Frederic98/LMI-Restore/LMI_GUI/Images/nut.jpg

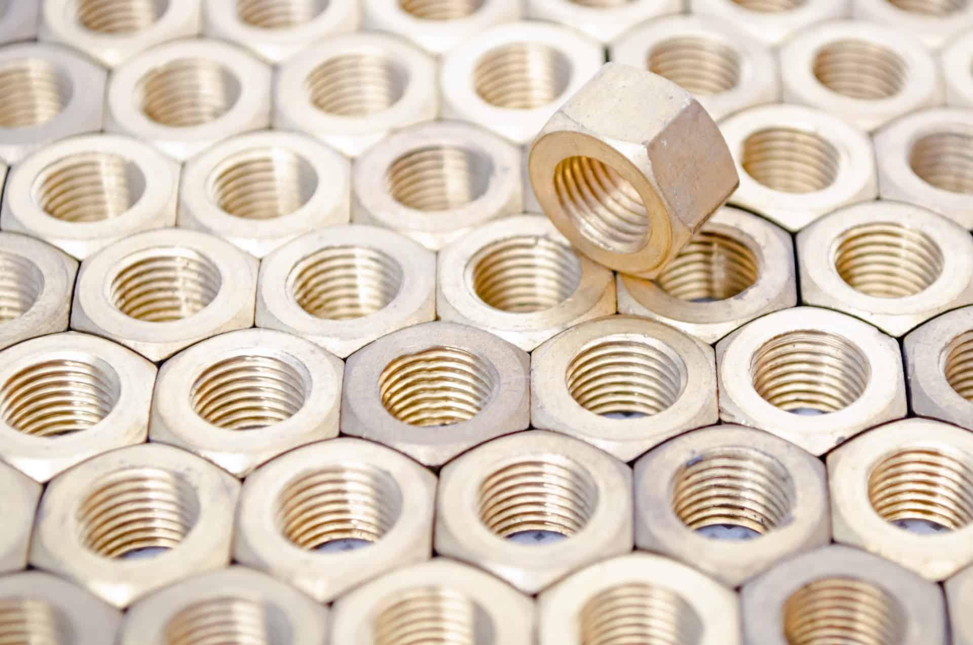
LMI_GUI/Images/nut.jpg
