Frederic98/LMI-Restore/LMI_GUI/Images/busy_1.PNG

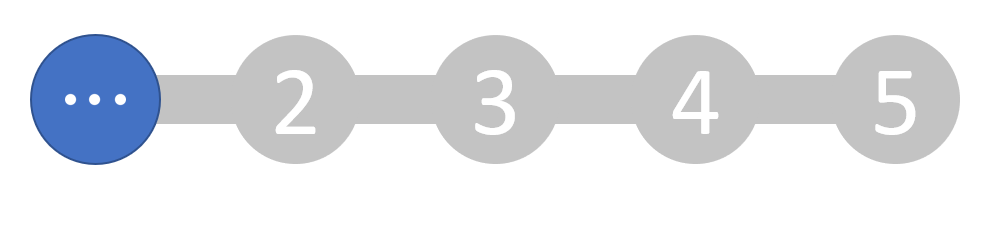
LMI_GUI/Images/busy_1.PNG
