Frederic98/LMI-Restore/LMI_GUI/Images/busy_3.PNG

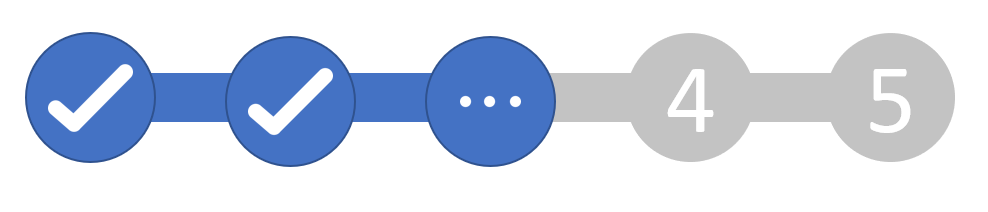
LMI_GUI/Images/busy_3.PNG
