Frederic98/LMI-Restore/LMI_GUI/Images/Storage unit empty robot side.png

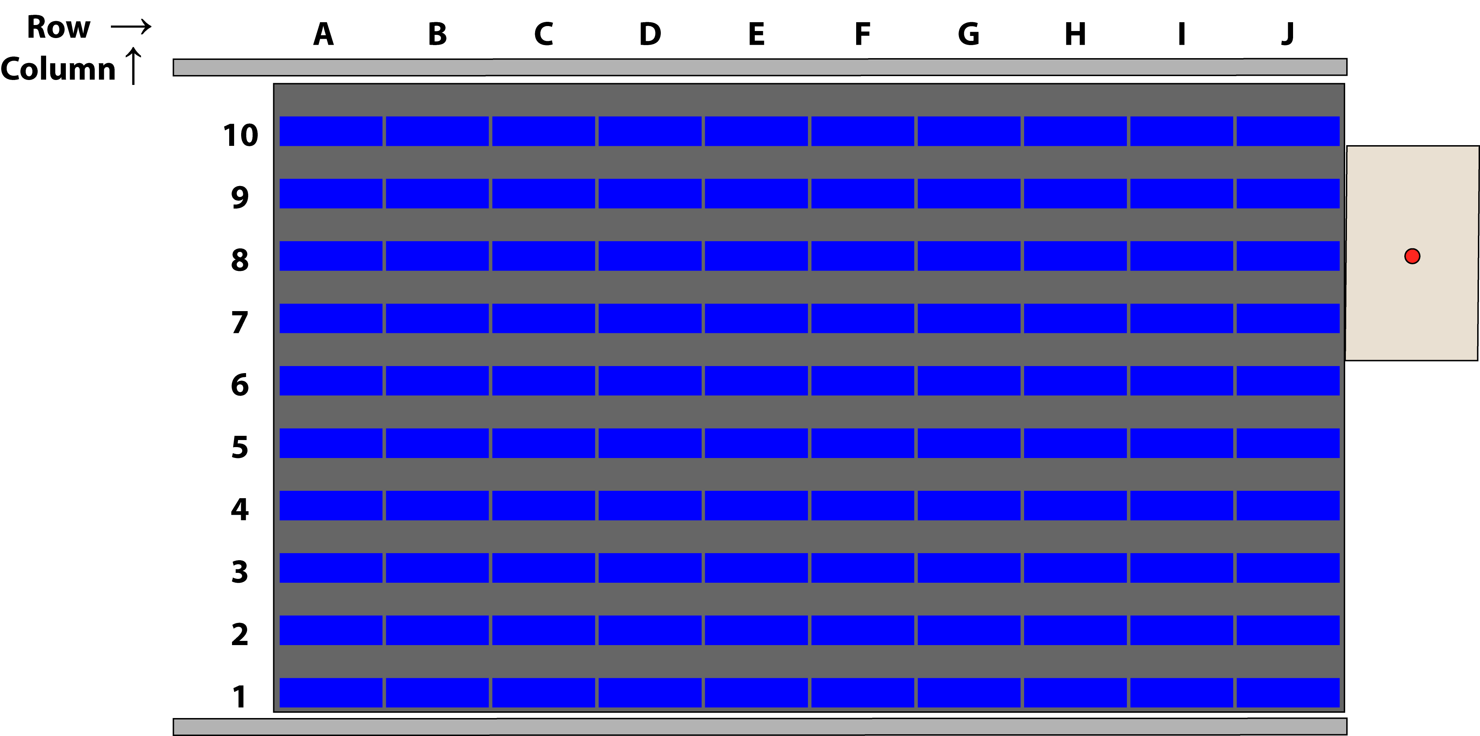
LMI_GUI/Images/Storage unit empty robot side.png
