Frederic98/LMI-Restore/LMI_GUI/Images/Triple-dot.png

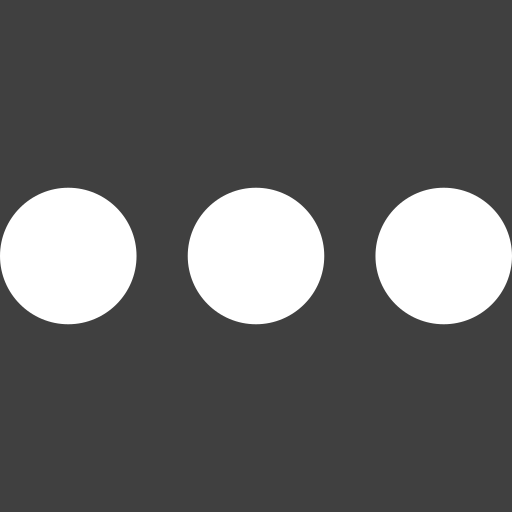
LMI_GUI/Images/Triple-dot.png
