Frederic98/LMI-Restore/CAD Files/CAD LMI/3D machining files/T00151-03D-R01.STL

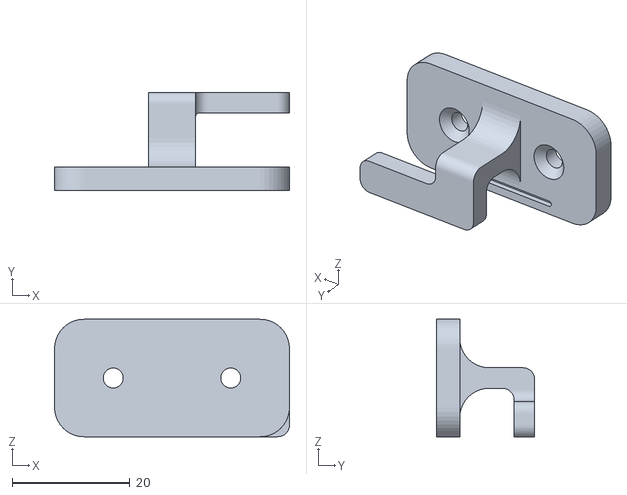
[picture p48: CAD file, 2019-02-02]
CAD Files/CAD LMI/3D machining files/T00151-03D-R01.STL
40.0 x 16.8 x 20.0
