Frederic98/LMI-Restore/CAD Files/CAD LMI/DXF/T00140-0A4-R00-1v1.DXF

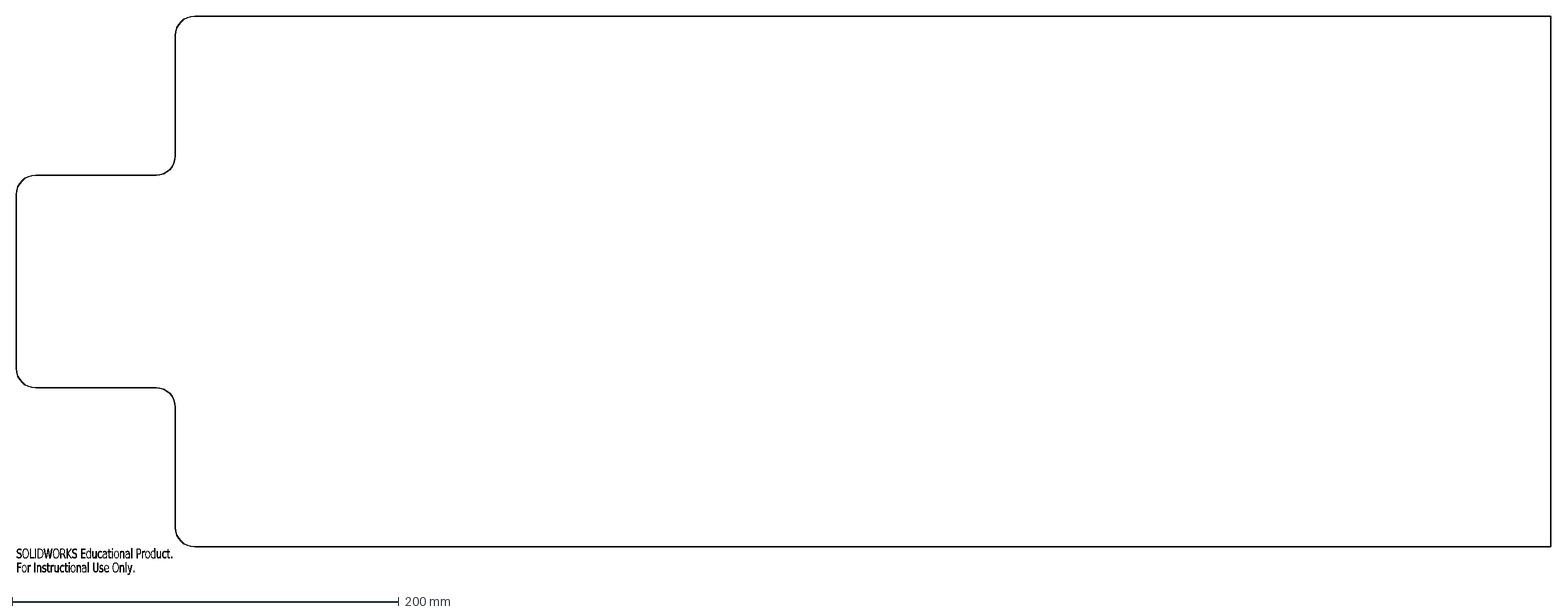
[picture p49: CAD file, 2019-02-02]
CAD Files/CAD LMI/DXF/T00140-0A4-R00-1v1.DXF
SOLIDWORKS Educational Product.
For Instructional Use Only.
