Frederic98/LMI-Restore/LMI_GUI/Images/verify-sign.png

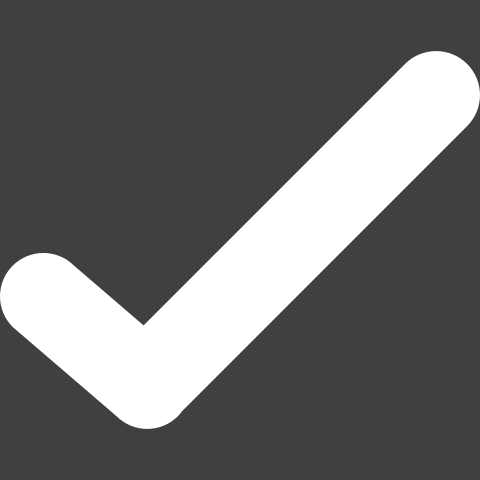
LMI_GUI/Images/verify-sign.png
