Frederic98/LMI-Restore/LMI_GUI/Images/verify-sign_green.png

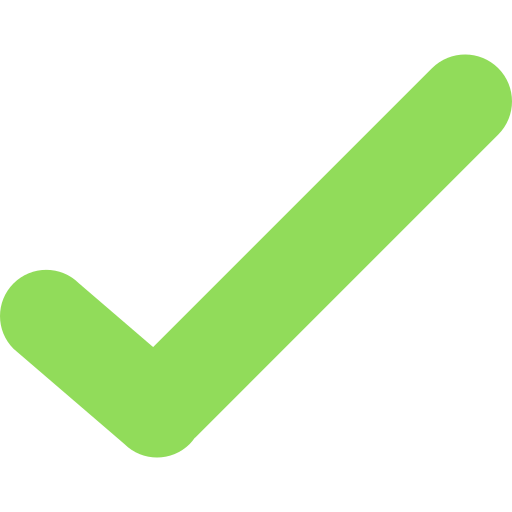
LMI_GUI/Images/verify-sign_green.png
