Frederic98/LMI-Restore/CAD Files/CAD LMI/Drawings/T00155-0A3-R00.pdf

37,50 | 15

200

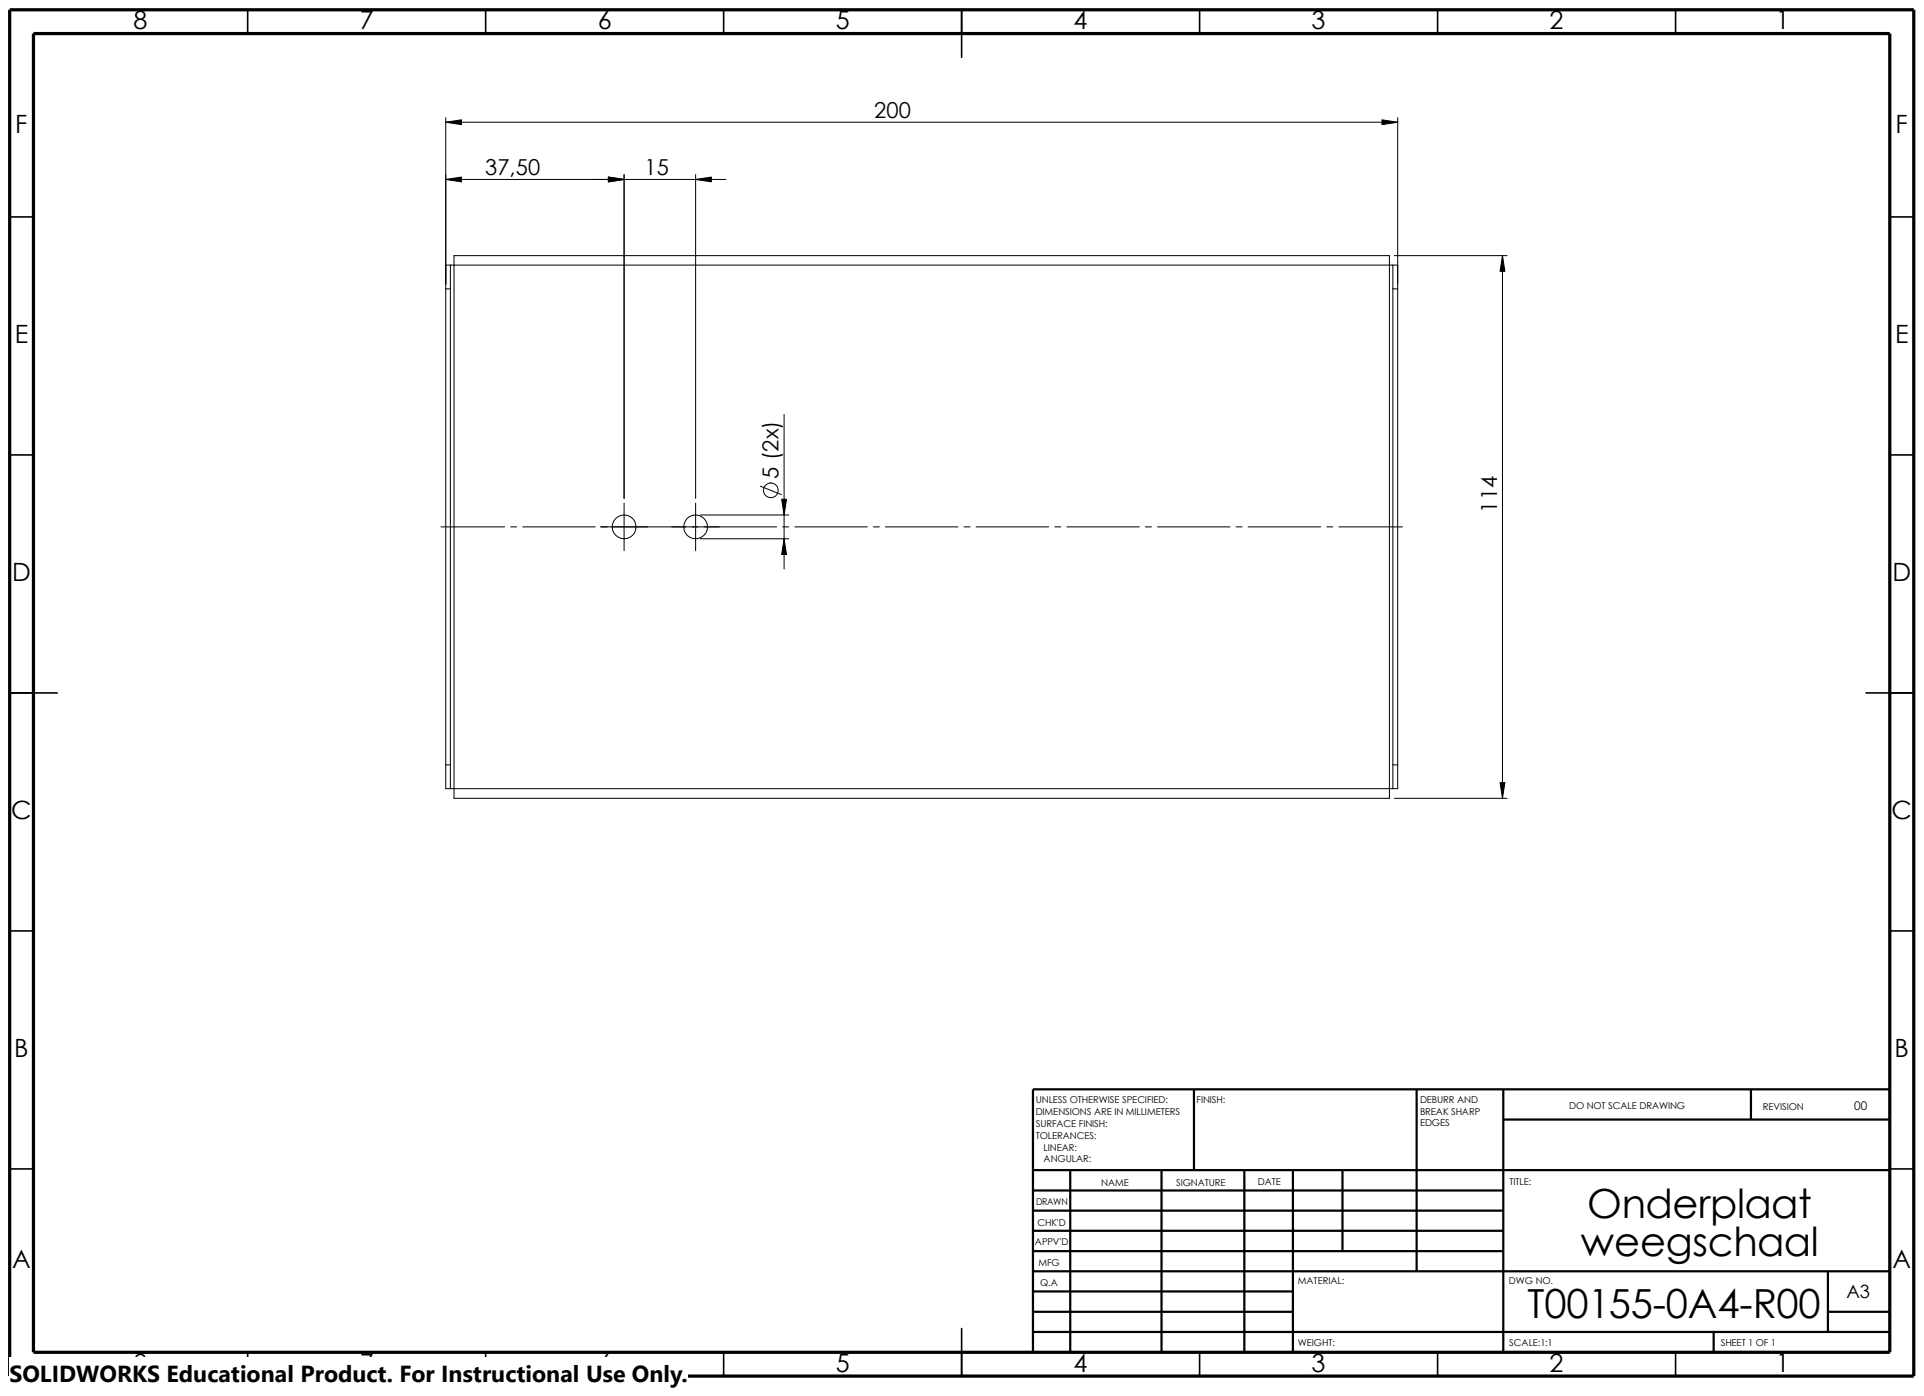
[picture p75: page 1]
SCALE:1:1; SHEET 1 OF 1; WEIGHT:; BREAK SHARP; weegschaal A; REVISION; FINISH:; EDGES; DEBURR AND

UNLESS OTHERWISE SPECIFIED:
DIMENSIONS ARE IN MILLIMETERS
SURFACE FINISH:
TOLERANCES:
LINEAR:
ANGULAR:

DO NOT SCALE DRAWING

NAME | SIGNATURE | DATE | | | | TITLE: Onderplaat

DRAWN

CHK'D

APPV'D

MFG

Q.A | | | | MATERIAL: | DWG NO. T00155-0A4-R00 | A3

SOLIDWORKS Educational Product. For Instructional Use Only.
