Frederic98/LMI-Restore/CAD Files/CAD LMI/Drawings/T00161-0A4-R00.pdf

3
2

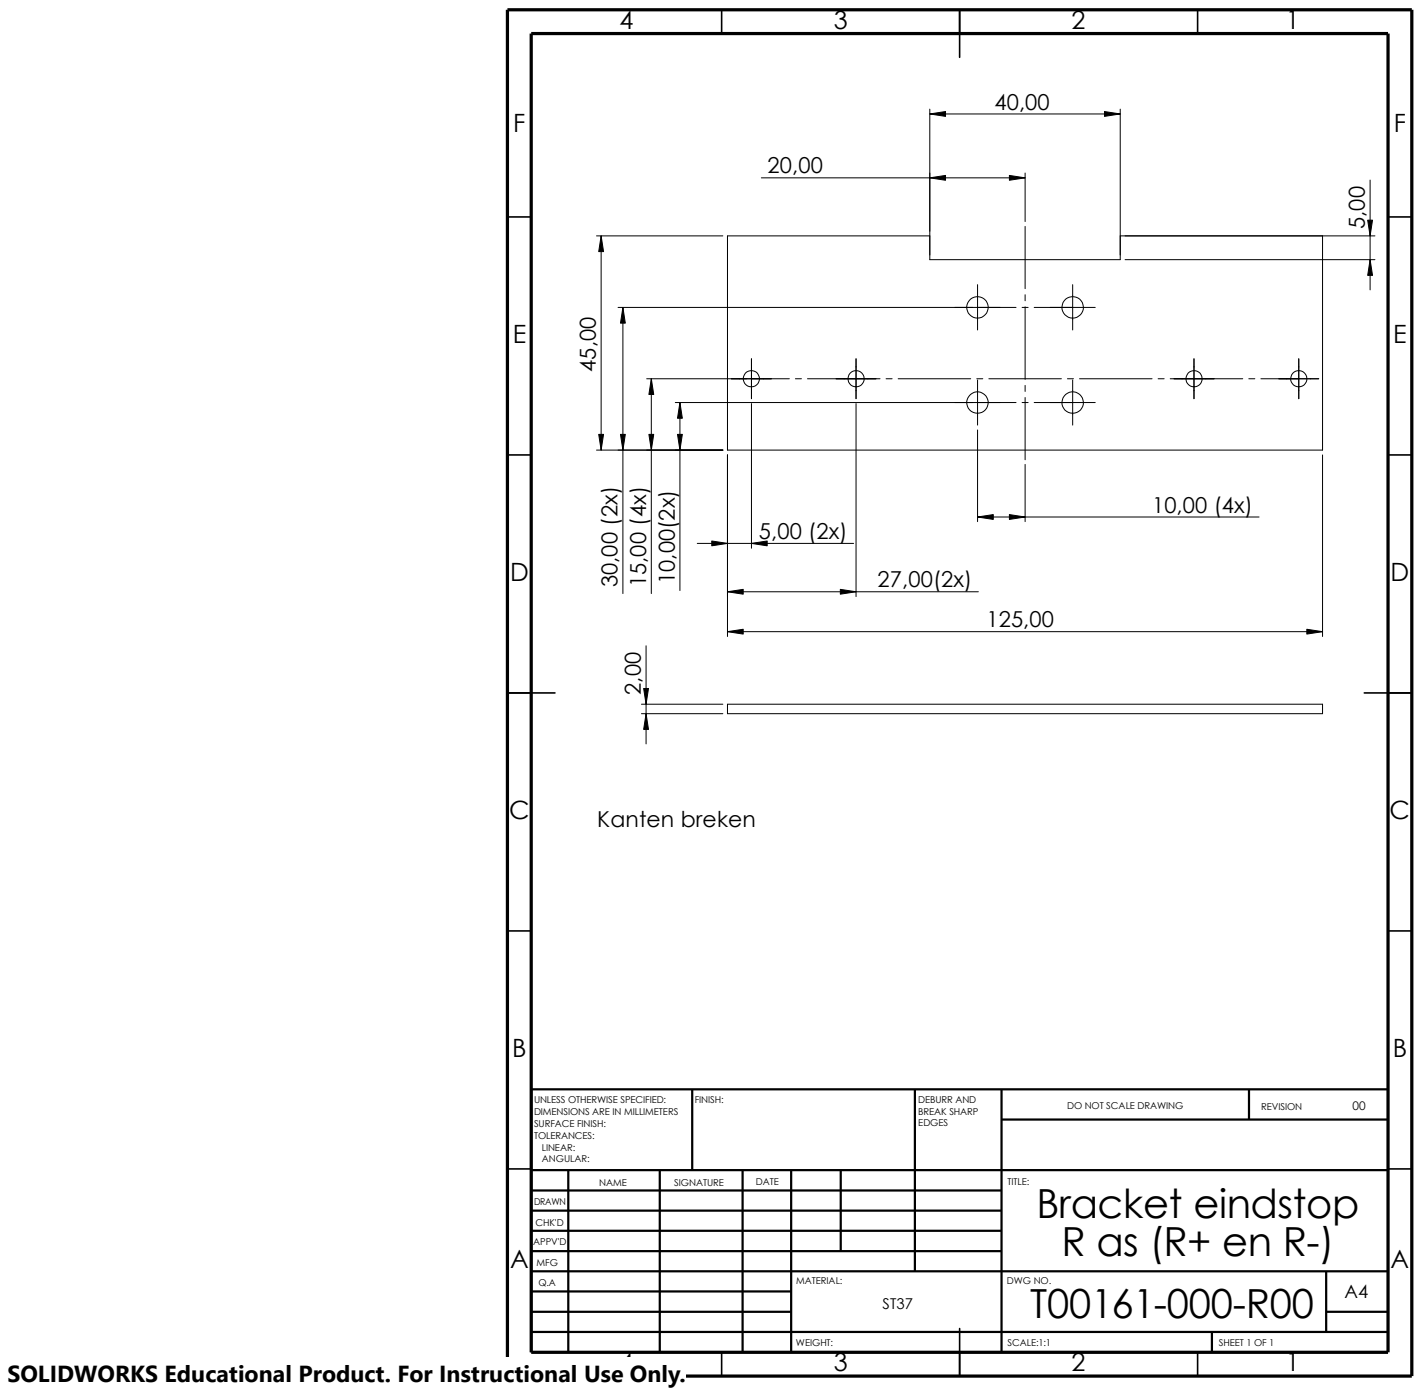
[picture p76: page 1]
Kanten breken; REVISION; DWG NO.; MFG; FINISH:; EDGES; MATERIAL:; SHEET 1 OF 1; SCALE:1:1; WEIGHT:; BREAK SHARP; DEBURR AND

UNLESS OTHERWISE SPECIFIED:
DIMENSIONS ARE IN MILLIMETERS
SURFACE FINISH:
TOLERANCES:
LINEAR:
ANGULAR:

DO NOT SCALE DRAWING

NAME | SIGNATURE | DATE | TITLE: Bracket eindstop R as (R+ en R-)

DRAWN

CHK'D

APPV'D

SOLIDWORKS Educational Product. For Instructional Use Only.
