Frederic98/LMI-Restore/CAD Files/CAD LMI/Drawings/T00167-0A4-R00.pdf

E E

F F

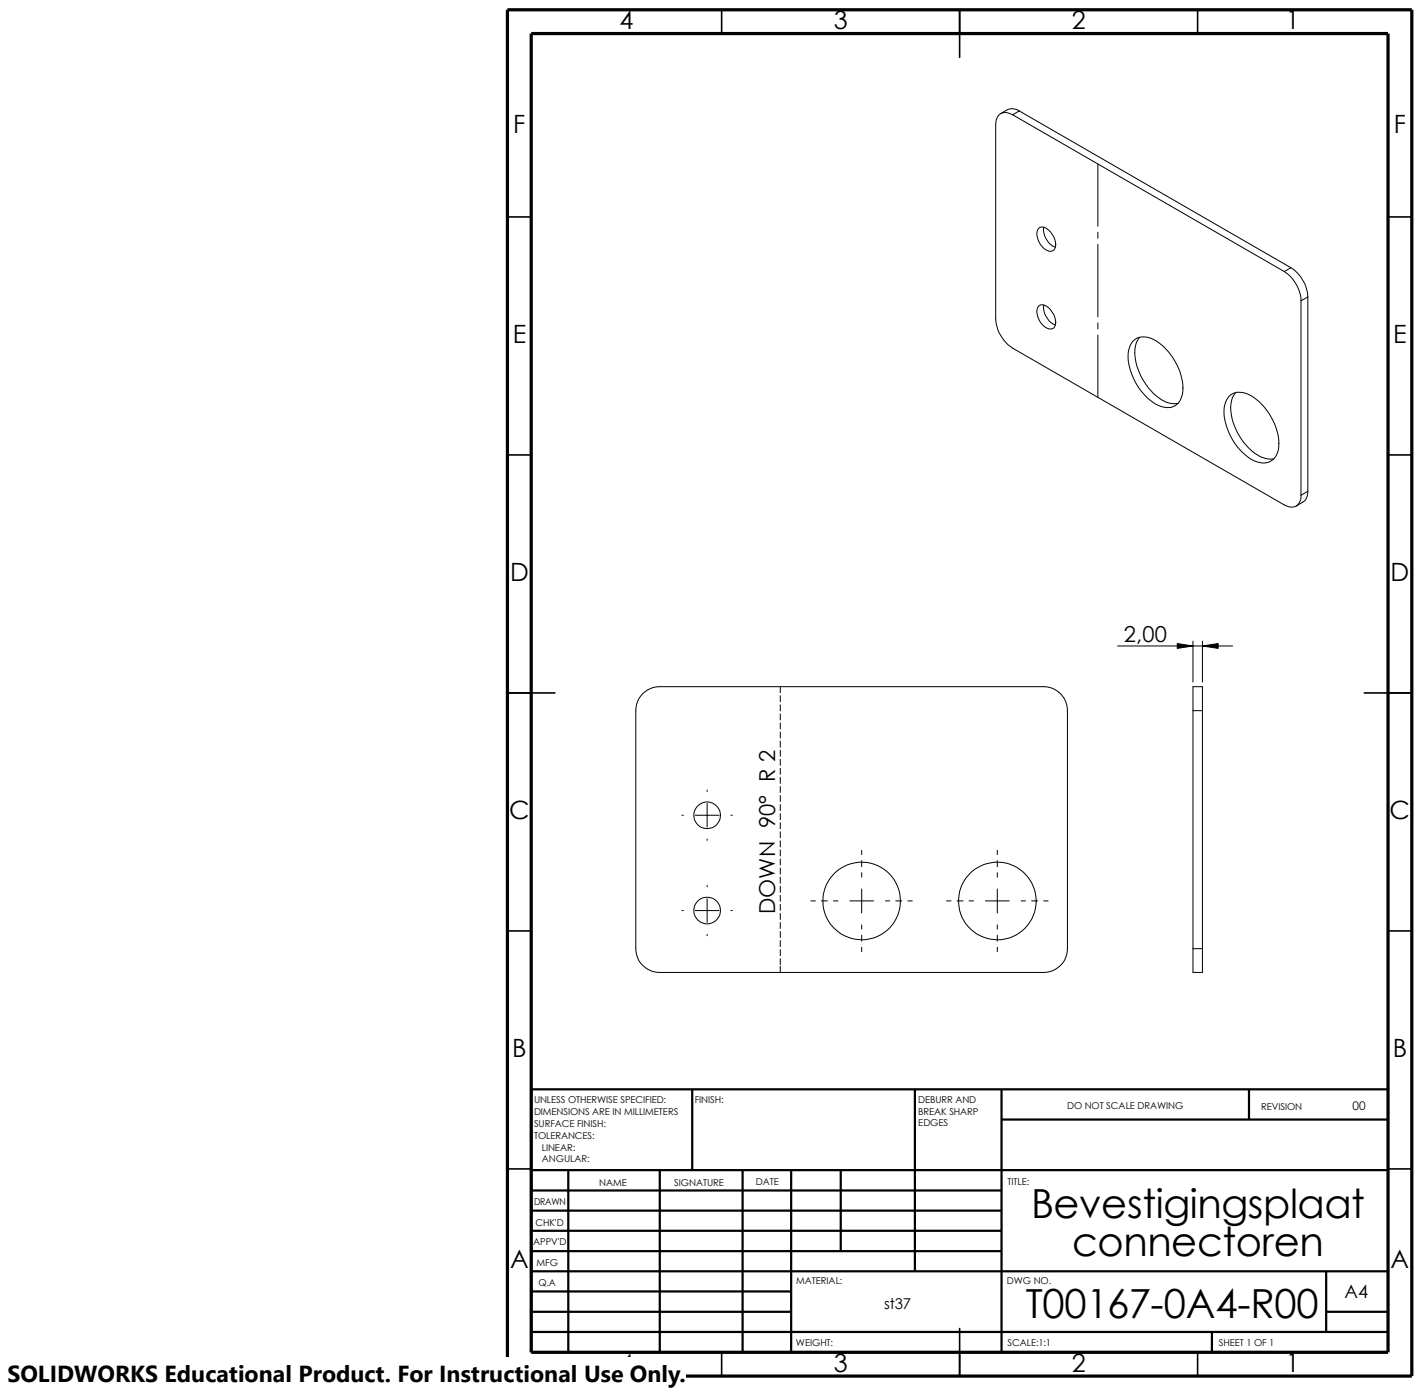
[picture p77: page 1]
BREAK SHARP; connectoren; SCALE:1:1; WEIGHT:; FINISH:; EDGES; SHEET 1 OF 1; REVISION; DEBURR AND; DOWN 90° R 2

UNLESS OTHERWISE SPECIFIED:
DIMENSIONS ARE IN MILLIMETERS
SURFACE FINISH:
TOLERANCES:
LINEAR:
ANGULAR:

DO NOT SCALE DRAWING

NAME | SIGNATURE | DATE | | | | TITLE: Bevestigingsplaat

DRAWN

CHK'D

APPV'D

MFG
Q.A | | | | MATERIAL: st37 | DWG NO. T00167-0A4-R00 | A4

SOLIDWORKS Educational Product. For Instructional Use Only.
