Frederic98/LMI-Restore/smart_storage/arduino/Move_it/GrabContainer.ino

void GrabContainer(){
  Serial.println("Grabbing container");
  Serial.println("Extending Arm");

  stepperZ.moveTo(Zconstant);

  while(stepperZ.distanceToGo() != 0){
    stepperZ.run();
  }

  Serial.println("Container reached");
  Serial.println("Hooking container");

  stepperY.moveTo(stepsY+Yconstant);

  while(stepperY.distanceToGo() != 0){
    stepperY.run();
  }

  Serial.println("Container hooked");
  Serial.println("retracting");

  stepperZ.moveTo(0);

  while(stepperZ.distanceToGo() != 0){
    stepperZ.run();
  }

  Serial.println("Container grabbed");

  stepsX= 0;
  stepsY= 0;  
}
